SchoenTom/skylive/docs/assets/exploded.png

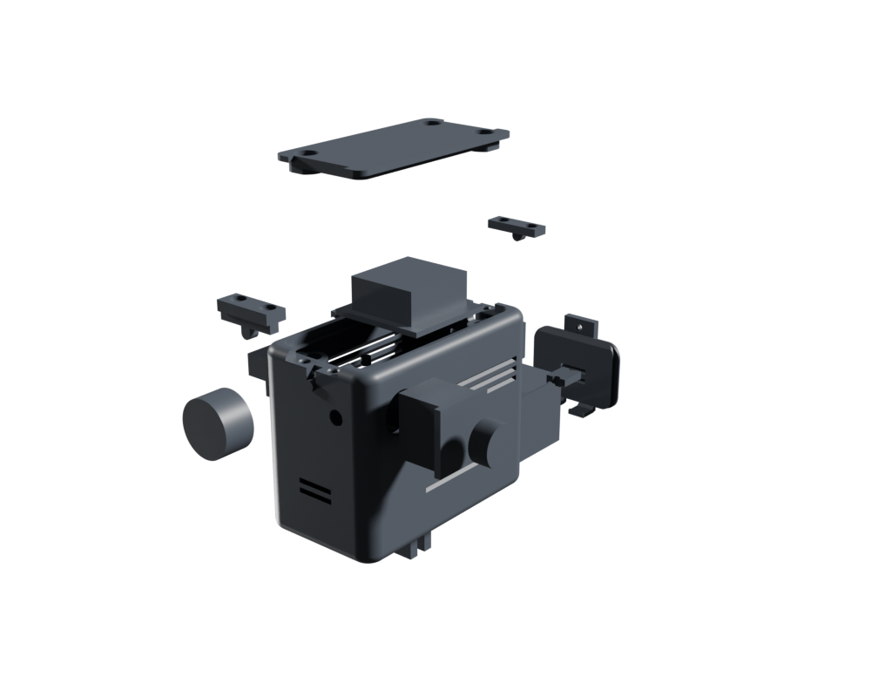
docs/assets/exploded.png
