SchoenTom/skylive/docs/assets/helix_hero.png

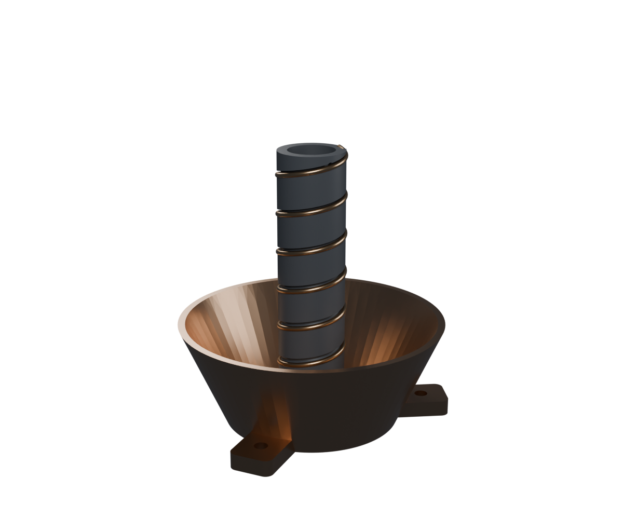
docs/assets/helix_hero.png
