SchoenTom/skylive/docs/og.png

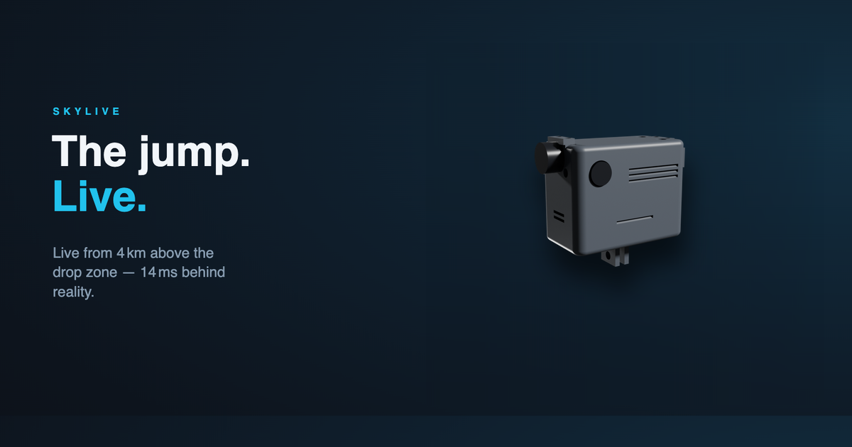
docs/og.png
