SchoenTom/skylive/docs/decks/poster_dual_components.png

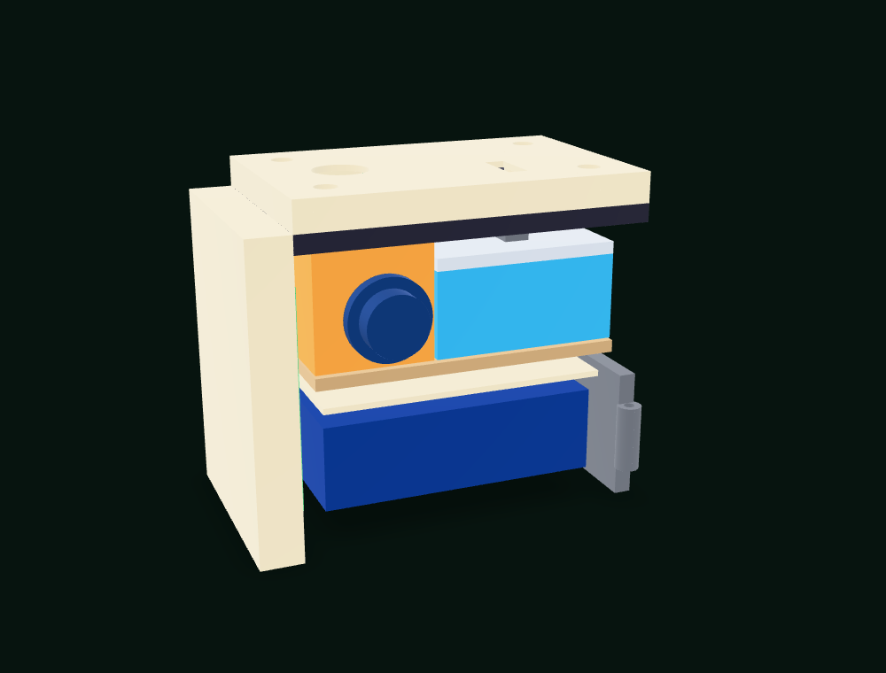
docs/decks/poster_dual_components.png
