SchoenTom/skylive/docs/poster_assembled_v3.png

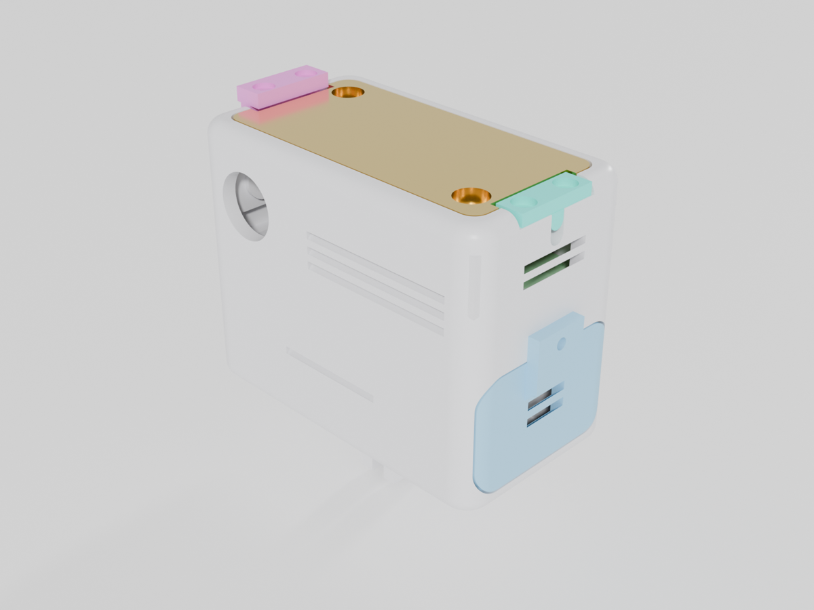
docs/poster_assembled_v3.png
